CogniPilot/spinali_mcxn_t1_shields/kicad/spinali_mcxn_t1_f9p/stackup/STK-95801-1.pdf

QR-ME-15(A)

## Engineering Confirmation Note Layer stackup & impedance

Subject :Questions about the stack and the impedance value From ：ShenZhen HaoBang Circuit Co., Ltd
Writer ：Key
Check ：Kevin
Pdctno ：8s90z00aa0
Cus NO ：STK-95801
DATE ：2025/07/10 08:24:30

## Stackup Information:

Layer | ER | Info | Thickness
TOP | ====================================== | 1/2 Oz+Plating=1.5mil
4.0 | PP | 2116 | 4.2 (mil)
L2 | ====================================== | 1 Oz=1.2mil
4.5 | Core | 1.23 mm | 48.43(mil)
L3 | ====================================== | 1 Oz=1.2mil
4.0 | PP | 2116 | 4.2(mil)
BOT | ====================================== | 1/2 Oz+Plating=1.5mil

111
Finished: | 62.23(+6.3/-6.3) mil | 1.59(+0.16/-0.16) MM
Designed: | 63mil | 1.6 MM
Material: | TU768 | TU768

## Impedance Information:

Ctrl | Ref | Imp_type | Cust_req | Imp_req | HB_des | Imp_des | mask | H1 | Er1 | H2 | Er2
L1 | L2 | Single-Ended | 6.8 | 50+/-10% | 6.8 | 50.47 | Yes | 4.2 | 4.0
L1 | L2 | Difference | 17.9/5.0 | 50+/-10% | 17.9/5.0 | 50.04 | Yes | 4.2 | 4.0
L1 | L2 | Difference | 5.8/5.2 | 90+/-10% | 5.8/5.2 | 90.25 | Yes | 4.2 | 4.0
L2 | L1/L3 | Single-Ended | 5.5 | 50+/-10% | 5.5 | 50.05 | | 48.43 | 4.5 | 5.4 | 4.0
L3 | L2/L4 | Single-Ended | 5.5 | 50+/-10% | 5.5 | 50.05 | | 48.43 | 4.5 | 5.4 | 4.0
L4 | L3 | Single-Ended | 6.8 | 50+/-10% | 6.8 | 50.47 | Yes | 4.2 | 4.0
L4 | L3 | Difference | 17.9/5.0 | 50+/-10% | 17.9/5.0 | 50.04 | Yes | 4.2 | 4.0
L4 | L3 | Difference | 5.8/5.2 | 90+/-10% | 5.8/5.2 | 90.25 | Yes | 4.2 | 4.0

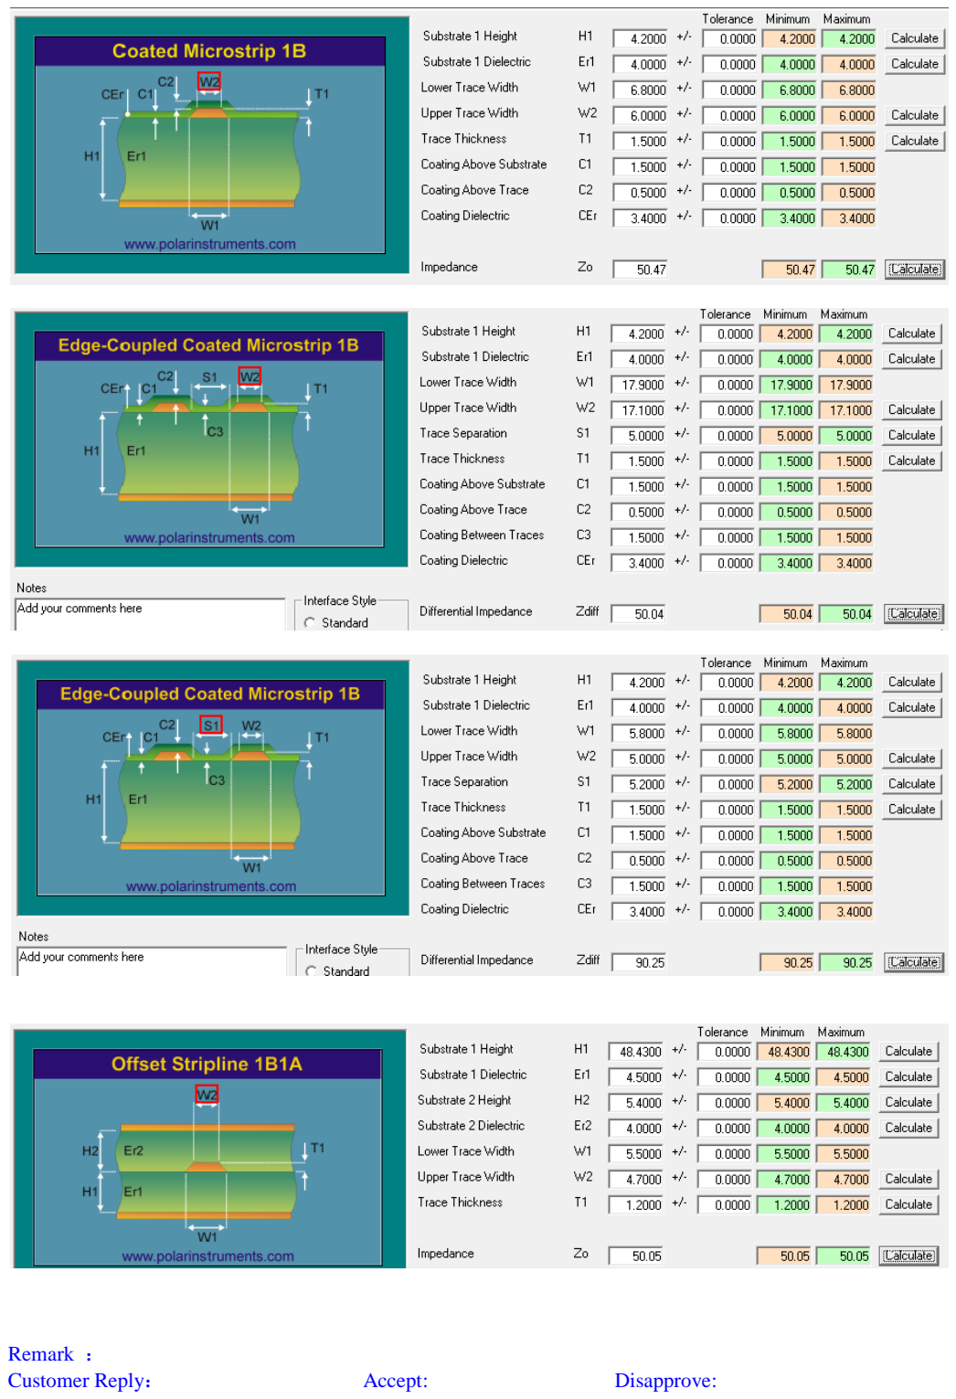
[picture p6: page 2]

Remark

：
Customer Reply
： | Accept: | Disapprove:

Date:

： | Signature

：
Mark

：
Remark

：
